less-smog/protoboard/images/1.jpg

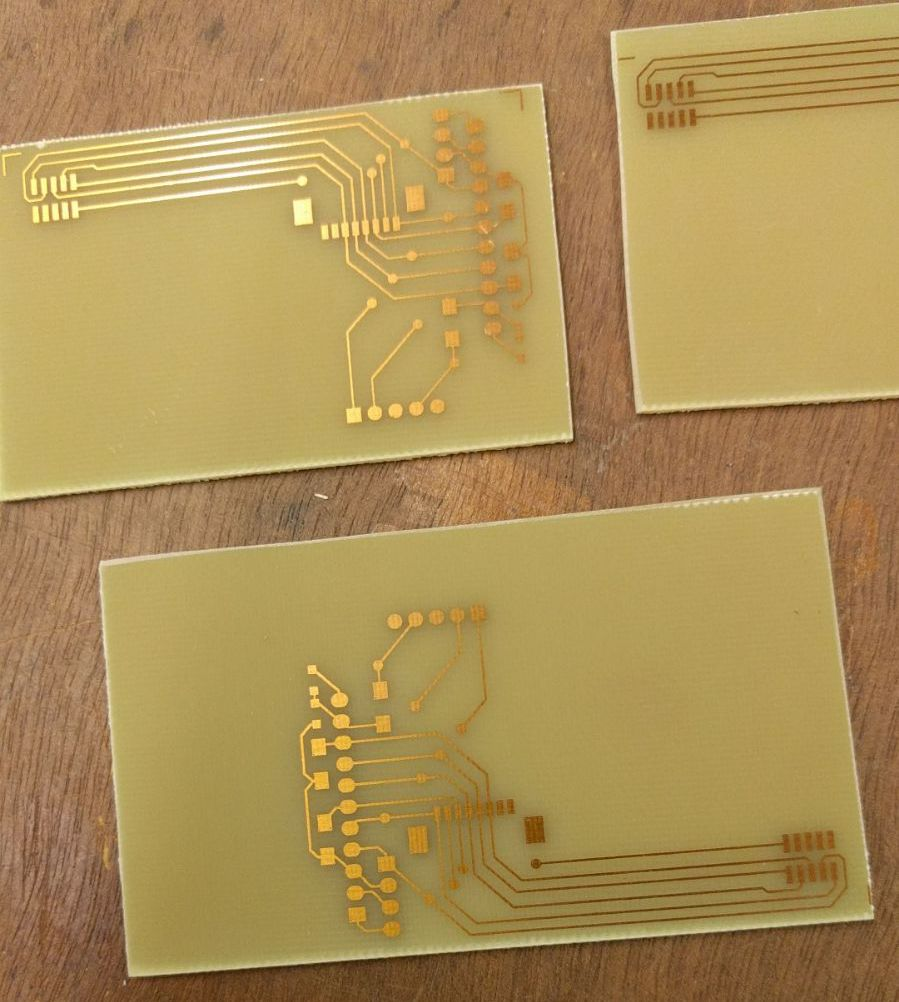
images/1.jpg
